wmsi/owl_dev/owl projects/Interlakes Martian Draft/martian_timer/martian_timer.ino

/* modified version of ticking_timer.ino. To stop the timer
 *  you have to connect three colored wires correctly.
 *  
 *  This sketch demos the use of the 7 segment serial display
 *  as used for the objective of a timer-based game involving
 *  the Owls. The timer may be the central focus of the game,
 *  which participants only find after solving a series of clues/
 *  directions with their "seeking" Owl unit.
 *  
 *  In this example, the timer runs from an allotted number
 *  of minutes down to 0:00. It can broadcast intermittent
 *  updates to the seeking Owls, and tell all searching units
 *  if it has been found or if time has run out. For some games,
 *  it may be desirable that the timer never actually runs down
 *  to zero- in this case the timer can be set to continually 
 *  restart with one minute left instead of running out of time.
 *  
 *  This sketch also demos the "push to beep" functionality of 
 *  these Owls. If the timer (hidden) unit receives a "push to beep"
 *  from a seeking unit it will play a series of beeps over the 
 *  speaker. Please note that with the conventional Owl board design
 *  you will need to solder an extra wire to the ground pin of the  
 *  speaker and run the other end to a "speaker enable" pin. More
 *  on this in the Comprehensive Owl Guide:
 *  
 *  https://docs.google.com/document/d/1dBl1U2nG0VlWLK2JO2t5rwEwFP2gaVT_iVvMPuYcGfo/
 *  
 */

#define GREEN   A0
#define YELLOW  A1
#define ORANGE  A2

#define BLUE    0
#define BLACK   512
#define WHITE   1023

// The 7 segment display talks to the microprocessor using the
// softwareSerial library.
#include <SoftwareSerial.h>

// Include the RFM69 and SPI libraries:
#include <RFM69.h>
#include <SPI.h>

// create a softwareSerial object to talk to the display
#define s7sTx     8
#define s7sRx     7
SoftwareSerial s7s(s7sRx, s7sTx);

// setup variables for updating the timer
#define RESTART     false     // restart the timer continually with one minute left
const int allotted_time = 20; //minutes
const int broadcast_interval = 30; //seconds
unsigned long last_update = 0;
unsigned long last_broadcast = 0;
unsigned long last_flash = 0;
boolean flash_state;
boolean stop_display = false;
unsigned int stop_time = 0;

// setup variables for the internal speaker
// SPEAKER_EN should be connected to the ground pin of the speaker
// when SPEAKER_EN is LOW (gnd) the speaker can make noise
#define CENTER_FREQ   2048    // resonant frequency
#define SPEAKER       3
#define SPEAKER_EN    9
boolean toggle = false;
boolean speaker_state = false;
int tone_length = 0;
int post_scale = 0;
int counter = 0;


// radio setup variables
#define MODESELECT    4
#define TRANSMIT      0
#define RECEIVE       1
static bool mode;

#define NETWORKID     0   // Must be the same for all nodes
static int MYNODEID;
static int TONODEID;

#define FREQUENCY     RF69_915MHZ

// Transmission power (0-31 = 5-20 dBm)
#define TXPOWER       31

// AES encryption (or not):
#define ENCRYPT       false // Set to "true" to use encryption
#define ENCRYPTKEY    "TOPSECRETPASSWRD" // Use the same 16-byte key on all nodes

// Use ACKnowledge when sending messages (or not)
// If ACK is set to true this sketch will send time updates over
// over until it receives an ACK from a seeking unit
#define USEACK        false // Request ACKs or not

RFM69 radio;


// All purpose button input. In this sketch it is only used
// to signal when the Owl is found
#define BUTTON    7

//turn Serial prints on or off. Sometimes Serial can cause errors
//when not connected to the computer, thoough this behavior has
//never been observed with Arduinos
#define SERIAL  true

void setup() {
  if(SERIAL)
    Serial.begin(9600);

  s7s.begin(9600);

  clearDisplay();

  pinMode(MODESELECT, INPUT);
  pinMode(SPEAKER, OUTPUT); 
  pinMode(SPEAKER_EN, OUTPUT);
  digitalWrite(SPEAKER_EN, HIGH);   // don't enable the speaker yet
  pinMode(BUTTON, INPUT_PULLUP);

  radioSetup();

}

/*
 * loop() updates the timer display, checks if a message has been 
 * received from the seeking units (in this example only push to 
 * beep works this way), if the hidden timer unit has been found 
 * (signalled by a button press), or if it's time to broadcast a time update
 */
void loop() {
  String send_string;
  String message = "";
  if (radio.receiveDone()) {
    message = printMessage();
  }

  // update countdown timer
  updateDisplay();
  
  // check for push to beep message
  if(message.indexOf("beep") != -1) {
    overwriteBeep();
  }

  // broadcast time update
  if((millis()-last_broadcast)/1000 >= broadcast_interval) {
    broadcastTime();
  }

  // check if button was pressed, signalling unit found
  if(digitalRead(BUTTON) == LOW) {
    radioSend("owl found");
    stop_display = true;
  }

  checkWires();
}

/*
 * check to see what's up with the input wires
 */
void checkWires() {
  int connection = 0;
  if(analogRead(GREEN) == BLUE) {
    connection++;
  }
  if(analogRead(YELLOW) > BLACK-2 && analogRead(YELLOW) < BLACK+2) {
    connection++;
  }
  if(analogRead(ORANGE) == WHITE) {
    connection++;
  }
  Serial.print(connection); Serial.println(" connections");
}
 

/*
 * This function enables the speaker and then plays a tone for 300 ms.
 * Tone can be played with the tone() function (which is louder but 
 * sometimes sees interference from softwareSerial) or with PWM via
 * analogWrite.
 */
void overwriteBeep() {
  digitalWrite(SPEAKER_EN, LOW);
  tone(SPEAKER,CENTER_FREQ,300);
//  analogWrite(SPEAKER, 127);
  digitalWrite(SPEAKER_EN, HIGH);
}

////////////////////////////// FUNCTIONS FOR THE 7 SEGMENT DISPLAY //////////////////////////

/*
 * updateDisplay() writes a new time to the display every second. Usually
 * this is just the allotted time - the amount of time the sketch has
 * been running. However, if RESTART has been set to true, the timer will
 * keep adding a minute instead of running down to 0.
 */
void updateDisplay() {
  if(millis() - last_update >= 1000) {
    int start_time = allotted_time*60;
    int elapsed_time = millis()/1000;
    int time_remaining = start_time - elapsed_time;
    while(RESTART && time_remaining < 0) {
      time_remaining += 60;
    }
    
    if(stop_display) {
      if(stop_time == 0)
        stop_time = start_time - elapsed_time;
      time_remaining = stop_time;
      flash_state = !flash_state;
    }
    
    unsigned int display_time = max((100*(time_remaining/60) + time_remaining%60),0);
    writeTime(display_time);
  }
}

/*
 * write a time to the display. display time must be an unsigned integer between
 * 0 and 9999. For most timer applications the last two digits should be less 
 * than 60. E.g. display_time = 549 -> 5:49
 */
void writeTime(unsigned int display_time) {
  char tempString[10];
  sprintf(tempString, "%4d", display_time);
  if(display_time < 60)
    tempString[1] = '0';
  if(display_time < 10)
    tempString[2] = '0';
  if(flash_state) {
    for(int i=0;i<4;i++)
      tempString[i] = '-';
  }
  s7s.print(tempString);
  setDecimals(0b00010000);
  last_update = millis();
}

/*
 * broadcast a time udpate to the seeking Owls. This function will get called
 * regularly as defined by broadcast_time. This function could also be used
 * to send clues to the seekers as the timer runs down.
 */
void broadcastTime() {
  if(SERIAL)
    Serial.println("sending time update");
  String send_string;
  int time_remaining = allotted_time - (millis()/60000);
  if(time_remaining <= 0) 
    send_string = "Out of time!";
  else
    send_string = String(String(time_remaining) + " min. left!");

  // keep trying on future iterations until ack received
  if(!USEACK || (USEACK &&radioSend(send_string))) {  
    last_broadcast = millis();
  }
}

// Turn on any, none, or all of the decimals.
//  The six lowest bits in the decimals parameter sets a decimal 
//  (or colon, or apostrophe) on or off. A 1 indicates on, 0 off.
//  [MSB] (X)(X)(Apos)(Colon)(Digit 4)(Digit 3)(Digit2)(Digit1)
void setDecimals(byte decimals)
{
  s7s.write(0x77);
  s7s.write(decimals);
}

// Send the clear display command (0x76)
//  This will clear the display and reset the cursor
void clearDisplay()
{
  s7s.write(0x76);  // Clear display command
}


/*
   Send out a message via the radio board. If USEACK is set to true,
   wait for an acknowledgment as dictated by sendWithRetry(). 
   From RFM69.h:
   sendWithRetry(uint8_t toAddress, const void* buffer, uint8_t bufferSize, 
                 uint8_t retries=2, uint8_t retryWaitTime=40);

   return true if an ACK was received
*/
bool radioSend(String send_string) {
  bool ack_recd = false;
  static int send_length = 0;
  static char send_buffer[RF69_MAX_DATA_LEN];

  send_length = min(send_string.length(),RF69_MAX_DATA_LEN);
  if(SERIAL) {
    Serial.print("sending to node "); Serial.print(TONODEID, DEC); Serial.print(", message: ");
    Serial.println(send_string);
  }
  for (byte i = 0; i < send_length; i++) {
    send_buffer[i] = send_string[i];
  }

  // There are two ways to send packets. If you want
  // acknowledgements, use sendWithRetry():
  if (USEACK) {
    if (radio.sendWithRetry(TONODEID, send_buffer, send_length, 1)) {
      if(SERIAL) {
        Serial.println("ACK received!");
        Serial.print("RSSI: "); Serial.println(radio.RSSI);
      }
      ack_recd = true;
    } else if(SERIAL) 
      Serial.println("No ACK received");
  } else {
    radio.send(TONODEID, send_buffer, send_length);
  } 
  return ack_recd;
}

/*
 * Process a new message from the radio board. Send ACK if ACK
 * is turned on, and print the message over Serial if SERIAL
 * is set to true. 
 */
String printMessage() {
  char message[radio.DATALEN + 1];
  // The actual message is contained in the DATA array,
  // and is DATALEN bytes in size:
  for (byte i = 0; i < radio.DATALEN; i++) {
    message[i] = (char)radio.DATA[i];
  }
  message[radio.DATALEN] = '\0';

  if (SERIAL) {
    Serial.print("received from node ");
      Serial.print(radio.SENDERID, DEC);
      Serial.print(", message: "); 
      Serial.println(message);
  }
  if (radio.ACKRequested()) {
    radio.sendACK();
    if (SERIAL)
      Serial.println("ACK sent");
  }
  return message;
}

/*
 * Initialize the radio board into transmit or receive mode.
 * By default, radio.setPowerLevel() is used to set the output
 * power as high as possible, and the radio is set to promiscuous 
 * mode. If you want a radio unit to only receive messages addressed
 * its node, get rid of the line radio.promiscuous().
 * 
 * The encryption option has been kept around from the example 
 * sketches for this board but probably isn't necessary for
 * Owl applications.
 *
 * Currently this sketch only contains code to run in receive mode, 
 * since adding support for the LCD and GPS overloads the DIO pins 
 * with softwareSerial definitions. To restore mode functionality 
 * simply add mode handling in loop() (e.g. if(mode == TRANSMIT) { ... } else {...})
 */
void radioSetup() {
  if (digitalRead(MODESELECT)) {
    mode = RECEIVE;
    MYNODEID = 1;
    TONODEID = 2;
  } else {
    mode = TRANSMIT;
    MYNODEID = 2;
    TONODEID = 1;
    //    Serial.print("Transmit Mode Selected");
  }
  //  if(SERIAL)
  //    Serial.print("Node "); Serial.print(MYNODEID,DEC); Serial.println(" ready");

  // Initialize radio
  radio.initialize(FREQUENCY, MYNODEID, NETWORKID);
  radio.setHighPower();    // Only for RFM69HCW & HW!
  radio.setPowerLevel(TXPOWER); // power output ranges from 0 (5dBm) to 31 (20dBm)

  // promiscuous mode allows this unit to receive all transmissions on the network
  radio.promiscuous();
  radio.encrypt(ENCRYPTKEY);

}
