wmsi/owl_dev/prototype code/Arduino/gps_lcd_test/gps_lcd_test.ino

#include <TinyGPS++.h>
#include <SoftwareSerial.h>
/*
 This example uses software serial and the TinyGPS++ library by Mikal Hart
 Based on TinyGPSPlus/DeviceExample.ino by Mikal Hart
 Modified by acavis
*/

// Choose two Arduino pins to use for software serial
// The GPS Shield uses D2 and D3 by default when in DLINE mode
#define GPSRX 5
#define GPSTX 4
#define LCDRX 7
#define LCDTX 6

#define LCD true

// The Skytaq EM-506 GPS module included in the GPS Shield Kit
// uses 4800 baud by default
int GPSBaud = 9600;

// Create a TinyGPS++ object called "gps"
TinyGPSPlus gps;

// create a softwareSerial object to interface with the LCD
// we can use the same Rx and Tx because GPS only transmits, while LCD only receives
SoftwareSerial lcdSerial(LCDRX,LCDTX); // Rx, Tx
// Create a software serial port called "gpsSerial"
SoftwareSerial gpsSerial(GPSRX, GPSTX);

void setup()
{
  // Start the Arduino hardware serial port at 9600 baud
  Serial.begin(9600);

  if(LCD)
    lcdSerial.begin(9600);
  // Start the software serial port at the GPS's default baud
  gpsSerial.begin(GPSBaud);

  Serial.println(F("DeviceExample.ino"));
  Serial.println(F("A simple demonstration of TinyGPS++ with an attached GPS module"));
  Serial.print(F("Testing TinyGPS++ library v. ")); Serial.println(TinyGPSPlus::libraryVersion());
  Serial.println(F("by Mikal Hart"));
  Serial.println();
  clearLCD();
}

void loop()
{
  // This sketch displays information every time a new sentence is correctly encoded.
  while (gpsSerial.available() > 0)
    if (gps.encode(gpsSerial.read())) {
      if(LCD)
        clearLCD();
      displayInfo();
    }

  // If 5000 milliseconds pass and there are no characters coming in
  // over the software serial port, show a "No GPS detected" error
  if (millis() > 5000 && gps.charsProcessed() < 10)
  {
    Serial.println(F("No GPS detected"));
    writeLine("No GPS detected", 1, 0);
    while(true);
  }
}

void displayInfo()
{
  String loc;
  Serial.print(F("Location: ")); 
  if (gps.location.isValid())
  {
    Serial.print(gps.location.lat(), 6);
    Serial.print(F(","));
    Serial.print(gps.location.lng(), 6);
    loc = String(String(gps.location.lat(), 5) + String(gps.location.lng(), 5));
  }
  else
  {
    Serial.print(F("INVALID"));
    loc = "invalid";
  }
  if(LCD) {
    writeLine("Location:", 1, 0);
    writeLine(loc, 2, 0);
  }

  Serial.print(F("  Date/Time: "));
  if (gps.date.isValid())
  {
    Serial.print(gps.date.month());
    Serial.print(F("/"));
    Serial.print(gps.date.day());
    Serial.print(F("/"));
    Serial.print(gps.date.year());
  }
  else
  {
    Serial.print(F("INVALID"));
  }

  Serial.print(F(" "));
  if (gps.time.isValid())
  {
    if (gps.time.hour() < 10) Serial.print(F("0"));
    Serial.print(gps.time.hour());
    Serial.print(F(":"));
    if (gps.time.minute() < 10) Serial.print(F("0"));
    Serial.print(gps.time.minute());
    Serial.print(F(":"));
    if (gps.time.second() < 10) Serial.print(F("0"));
    Serial.print(gps.time.second());
    Serial.print(F("."));
    if (gps.time.centisecond() < 10) Serial.print(F("0"));
    Serial.print(gps.time.centisecond());
  }
  else
  {
    Serial.print(F("INVALID"));
  }

  Serial.println();
}


void clearLCD() {
  lcdSerial.write(254); // move cursor to beginning of first line
  lcdSerial.write(128);

  lcdSerial.write("                "); // clear display
  lcdSerial.write("                ");
  delay(50);
}

void writeLine(String str, int line, int pos) {
  char temp[16] = "               ";
  int num_chars = str.length();
  lcdSerial.write(254); // move cursor to beginning of first line
  switch(line) {
    case 2:
      lcdSerial.write(191+pos);
    case 1:
      lcdSerial.write(128+pos);
  }
  delay(10);
  for(int i=0; i<num_chars; i++) {
    temp[i] = str[i];
  }
  lcdSerial.write(temp);
  delay(100);
}
